georgsnarbuts/riga65/PROJECT PHOTOS/1.png

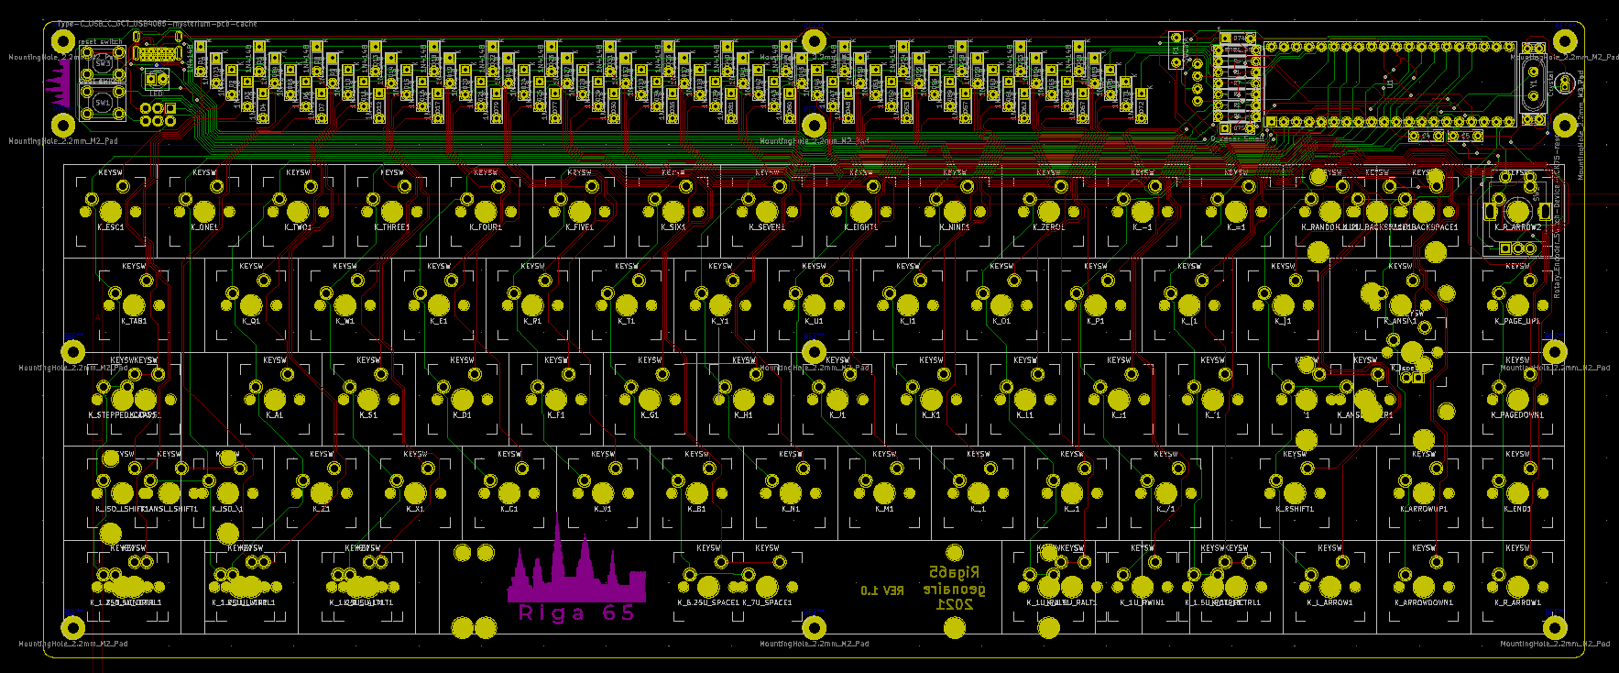
PROJECT PHOTOS/1.png
