georgsnarbuts/riga65/PROJECT PHOTOS/2.png

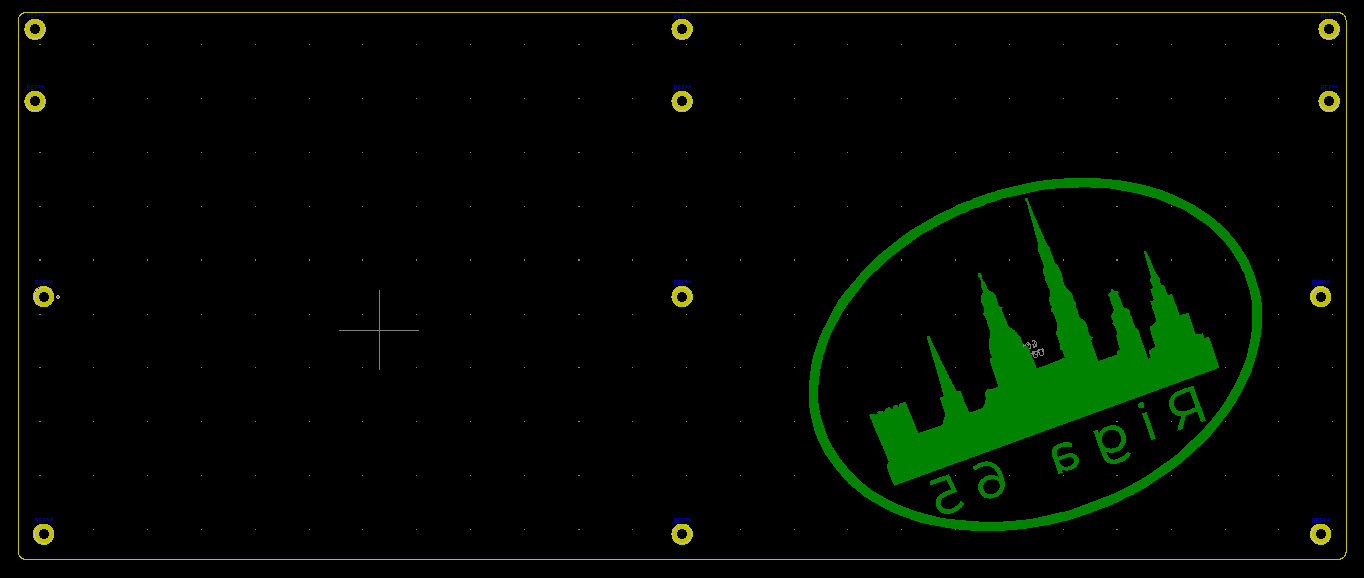
PROJECT PHOTOS/2.png
