georgsnarbuts/riga65/PROJECT PHOTOS/3.png

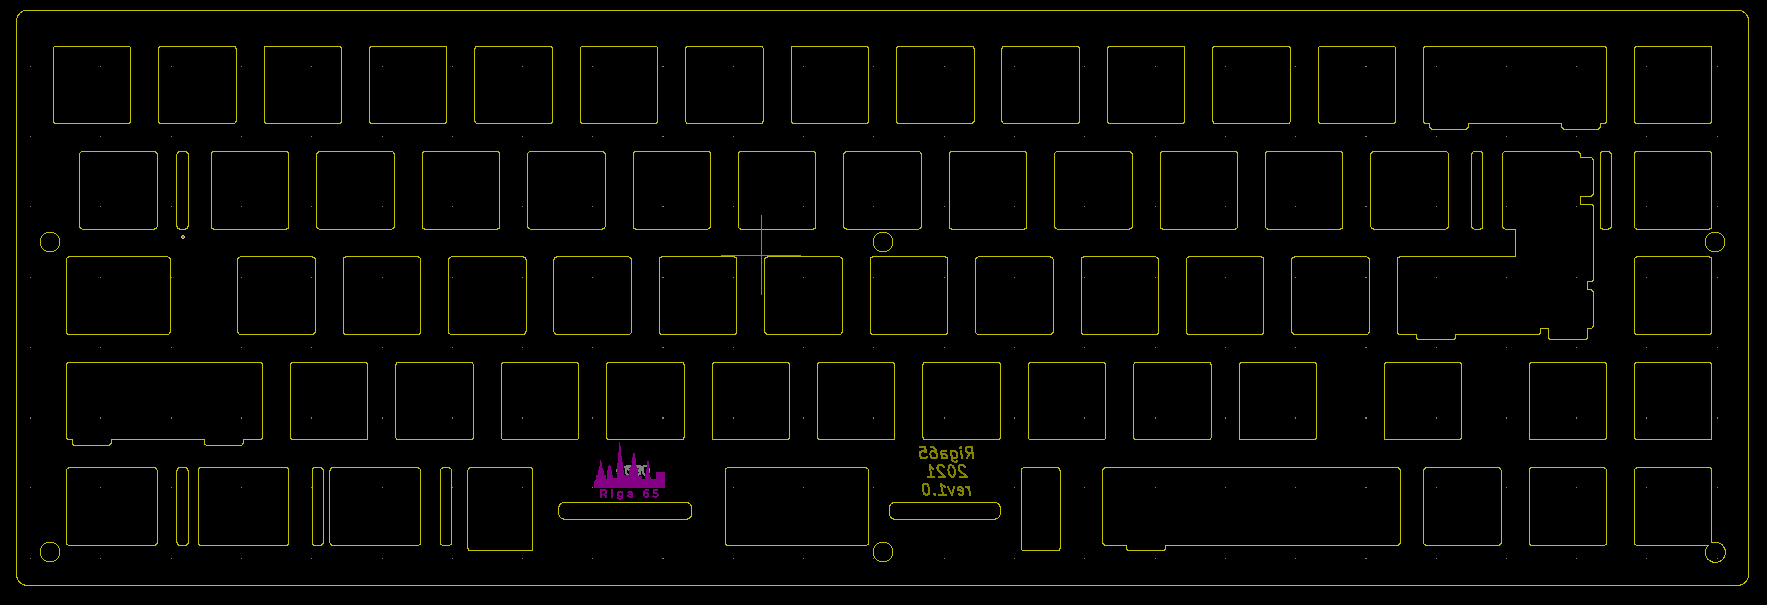
PROJECT PHOTOS/3.png
